MasatoKubotera/GankenKun_3DPrintParts/PLA/コックピット/コックピット_スライドロックカバー.stl

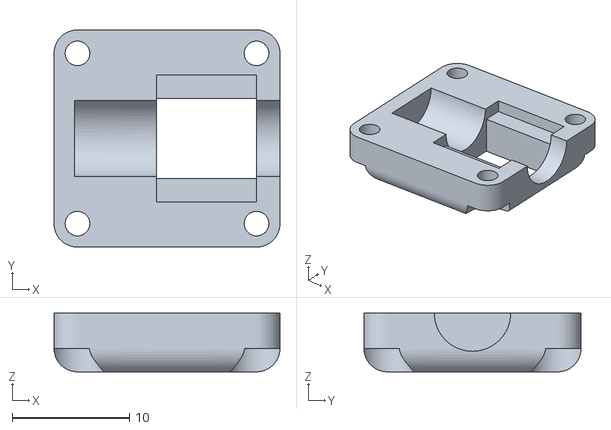
[picture p46: CAD file, 2021-01-02]
PLA/コックピット/コックピット_スライドロックカバー.stl
19.2 x 18.5 x 5.00
